niknabno/openbook/scad/top.scad

$fn = 90;

include<consts.scad>;
include<modules.scad>;

//---start override global consts---//
h = 2;

BAT_W = 62.5;
BAT_H = 77.5;

//cutoutL = 150;
//cutoutW = 200;
//cutoutH = 6;

sqrSupportZ = -h/3-KB_PLATE_W;
sqrSupportH = 21;

//Square supports prevent the walls from flexing
SQR_SUPPORT_L = 10;
LARGE_SQR_SUPPORT_W = 15;

//---end override global consts---//

difference() {
    minkowski() {
        cube([l, w, h], center=true);
    };
    //wall w/hinges is 1.5mm thicker
    translate([-l/2-1, w/2-3, -5]) cube([l+5,w,10]);

	for(i = [0 : 1]) {
            //Inset
            translate([-BAT_X_OFFSET-BAT_HOLES_DISTANCE/2, -w/2+51.25, -10])
            cube([BAT_W, BAT_H, 20], center=true);
            translate([BAT_X_OFFSET+BAT_HOLES_DISTANCE/2, -w/2+51.25, -10])
            cube([BAT_W, BAT_H, 20], center=true);
      }


     translate([-40, 65, -5]) linear_extrude(10) text("VOID_HEART", size=18, spacing=1.16, halign="center", font =  "Plaster:style=Regular");

        //---start intake on east side---//
    	for(a = [0 : 1 ]) {
        	for(i = [0 : 4]) {
            		translate([(i*11)+LAPTOP_EAST-73, (a*20.5)+55, -20]) largeIntake();
        	}
    	}
        for(a = [0 : 1 ]) {
        	for(i = [0 : 4]) {
            		translate([(i*11)+LAPTOP_EAST-67, (a*20.5)+65, -20]) largeIntake();
        	}
    	}
	//---end intake on east side---//


        //---start intake on west side--//
        for(a = [0 : 1 ]) {
        	for(i = [0 : 2]) {
            		translate([(i*11)+LAPTOP_WEETBIX+40, (a*20.5)+25, -20]) rotate(0) largeIntake();
        	}
    	}

        for(a = [0 : 1 ]) {
        	for(i = [0 : 2]) {
            		translate([(i*11)+LAPTOP_WEETBIX+32.5, (a*20.5)+15, -20]) rotate(0) largeIntake();
        	}
    	}
	//---end intake on west side---//


        //---start intake in centre---//
        for(a = [0 : 1 ]) {
        	for(i = [0 : 2]) {
            	translate([(i*11)-40, (a*20.5)+25, -20]) rotate(0) largeIntake();
        	}
    	}

        for(a = [0 : 1 ]) {
        	for(i = [0 : 2]) {
            	translate([(i*11)-47.5, (a*20.5)+15, -20]) rotate(0) largeIntake();
        	}
    	}
	//---end intake in centre---//


	//corner m3 holes
        cornerSqr(-l/2, -w/2-0.5);
        cornerSqr(l/2-12, w/2-12-0.5);
        cornerSqr(l/2-12, -w/2-0.5);
        cornerSqr(-l/2, w/2-12-0.5);

	//extra m3 holes north
        translate([0, LAPTOP_NORTH-sqrSupportW-1.85-1, sqrSupportZ]) m3Hole();
        translate([0, LAPTOP_SOUTH+sqrSupportW-0.5, sqrSupportZ]) m3Hole();

	//extra m3 holes equator
        translate([LAPTOP_WEETBIX + LARGE_SQR_SUPPORT_W/2-2, -0.5, sqrSupportZ]) m3Hole();
        translate([LAPTOP_EAST-LARGE_SQR_SUPPORT_W/2+2, -0.5, sqrSupportZ]) m3Hole();
        translate([0, -0.5, -3]) m3Hole();

	//extra m3 holes south
	translate([75-TRI_SUPPORT_W/2*1.25, w/2-TRI_SUPPORT_L/2-0.5, -3]) m3Hole();
	translate([-68-TRI_SUPPORT_W/2*1.25, w/2-TRI_SUPPORT_L/2-1, -3]) m3Hole();



	//--start screw indent for hinges//
	translate([HINGE_AX, LAPTOP_NORTH-8, -3]) screwIndent();
	translate([HINGE_AX+36, LAPTOP_NORTH-8, -3]) screwIndent();

	translate([HINGE_CX, LAPTOP_NORTH-8, -3]) screwIndent();
	translate([HINGE_CX+36, LAPTOP_NORTH-8, -3]) screwIndent();

	translate([HINGE_BX, LAPTOP_NORTH-8, -3]) screwIndent();
	translate([HINGE_BX+26, LAPTOP_NORTH-8, -3]) screwIndent();
	//--end screw intent for hinges--//

        //allow IEC socket to fit
        translate([-l/2-1, IEC_Y-3, -5]) cube([6, IEC_W+6, IEC_H]);

        //allow edp cable
        translate([-62+11, w/2-4, -4]) cube([18, 1.25, IEC_H]);

	//for voltometre
	translate([VOLTO_X+5.5, VOLTO_Y-0.5, -2])
	{
		cube([VOLTO_L+1, VOLTO_W+1, VOLTO_H+1]);
	}

       }

module m3Hole() {
     translate([0,0,2.917]) cylinder(95, 3, 3);
     cylinder(25, 1.85, 1.85, center=true);
}

module screwIndent()
{
	translate([0,0,2.917]) cylinder(95, 3, 3);
}

module largeIntake() {
    cylinder(25, LARGE_INTAKE_R, LARGE_INTAKE_R, $fn = 6);
}

//Designed to support KB+TP & M3 heatpress threaded inserts.
module cornerSqr(x, y) {
      translate([x+6,y+6, 30]) cylinder(95, 1.85, 1.85, center=true);
      translate([x+6,y+6, 0.25]) cylinder(95, 3, 3);

}
