niknabno/openbook/scad/topWithKB.scad

$fn = 90;

include<consts.scad>; //include global vars
include<modules.scad>; //include modules
